sathyavikram/cord-storage-reel/media/images/3-4.png

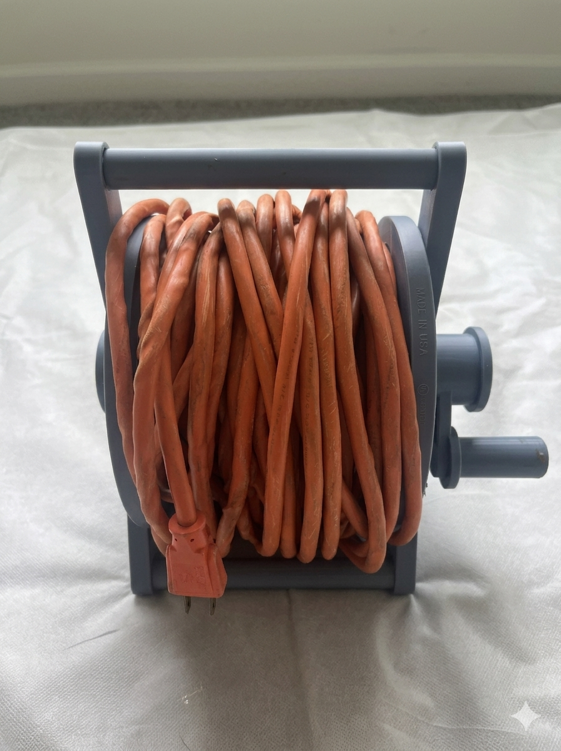
media/images/3-4.png
