sathyavikram/cord-storage-reel/media/images/4-3.png

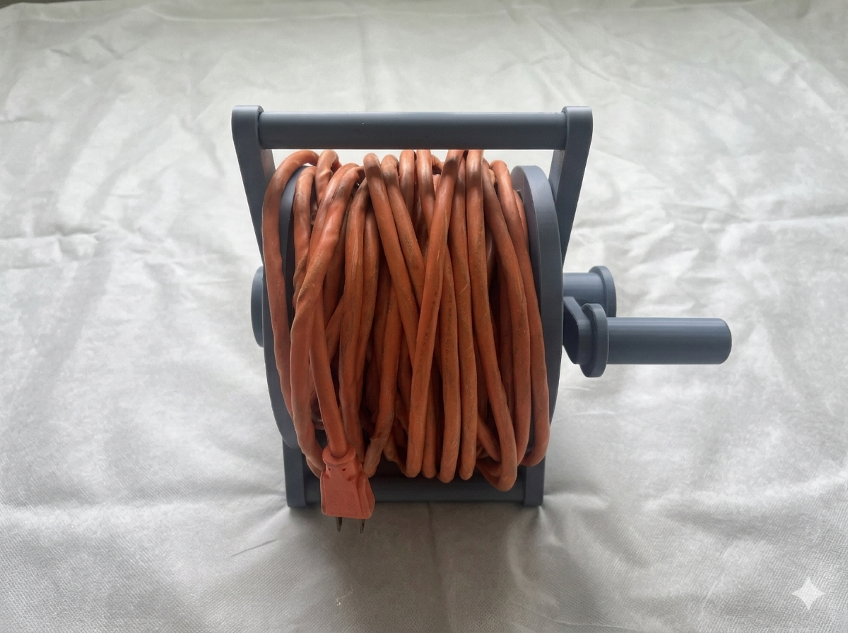
media/images/4-3.png
