sathyavikram/cord-storage-reel/media/images/IMG_8871.jpg

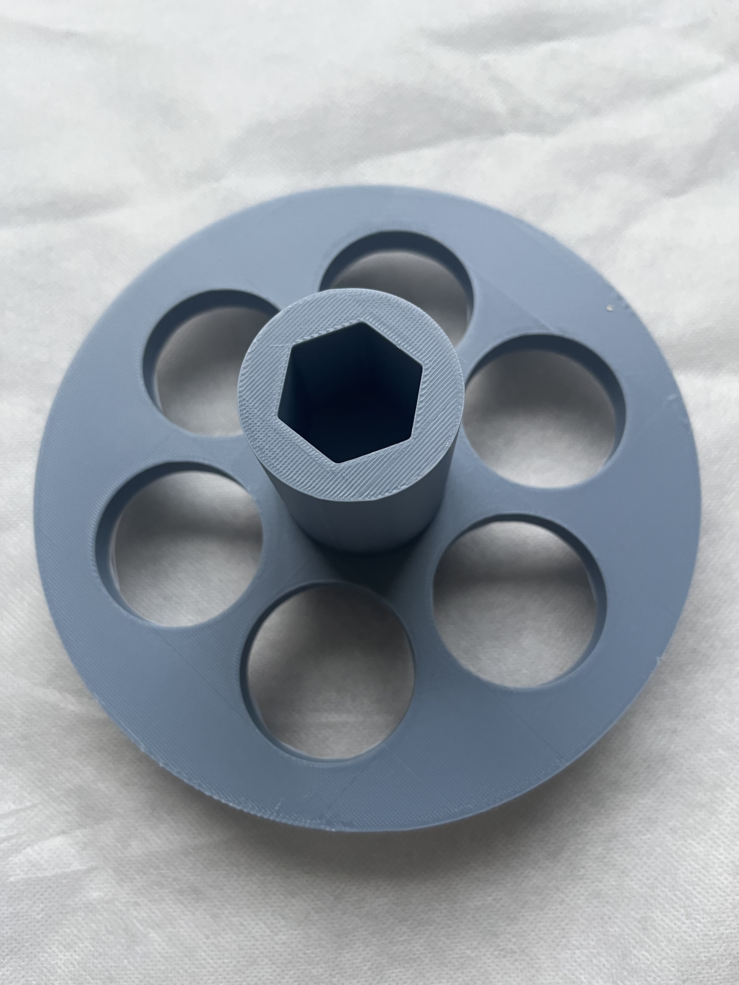
media/images/IMG_8871.jpg
