sathyavikram/cord-storage-reel/media/images/IMG_8883.jpg

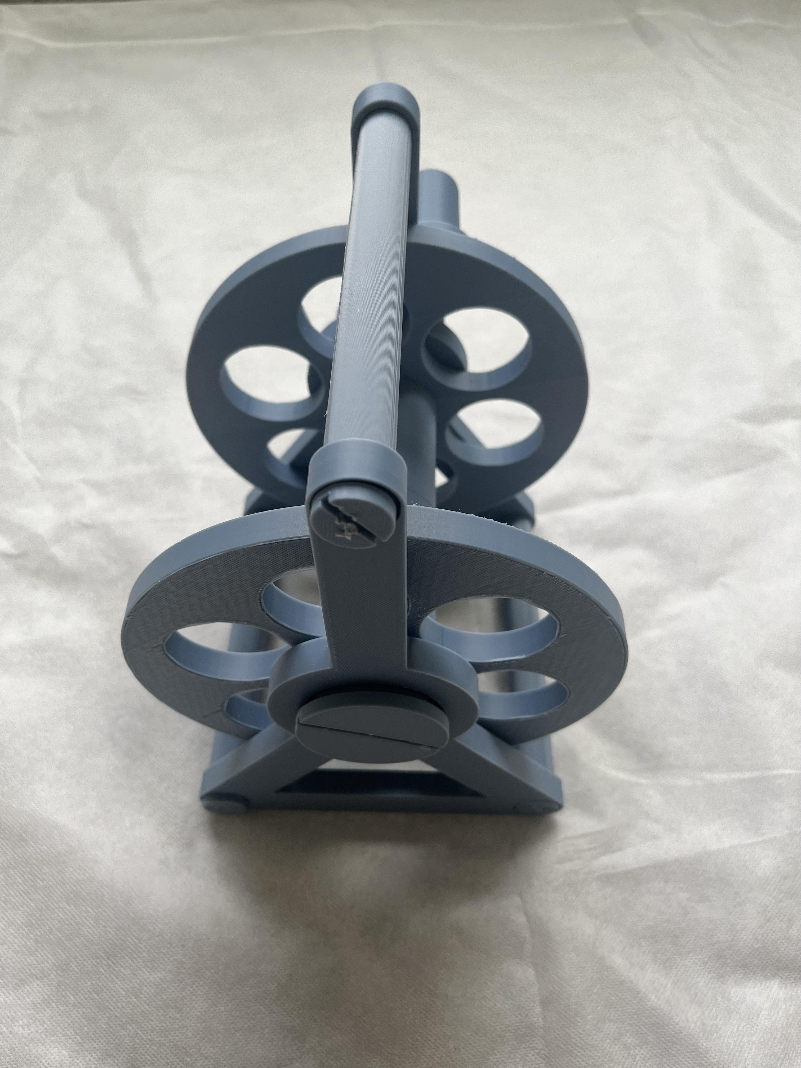
media/images/IMG_8883.jpg
