sathyavikram/cord-storage-reel/reference1.png

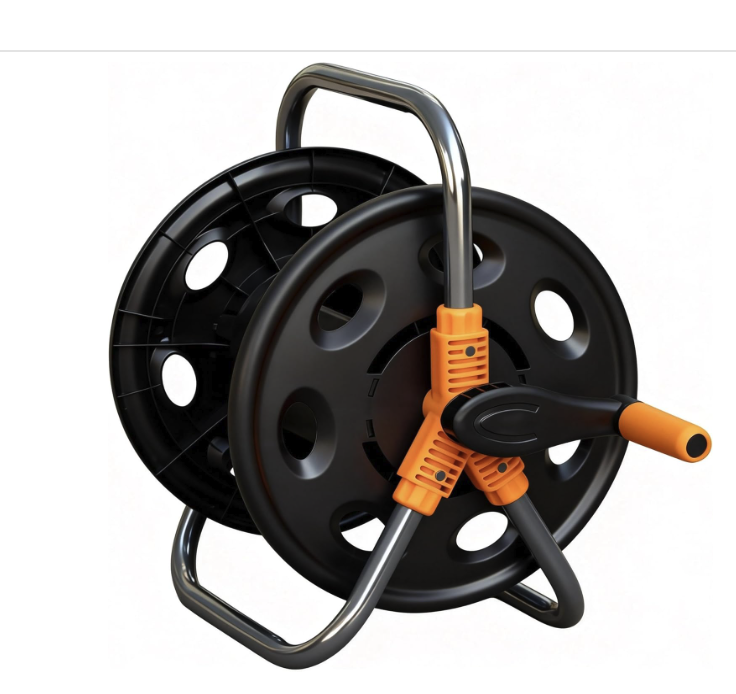
reference1.png
